monero-project/kastelo/hardware/utilities/ziftosma/README.md

## ZIF/SMA breakout board

This is a ZIF connector to SMA connector breakout board, for testing the NFC and BT antennas.

The following layer definition is used:
<br />
boardname.GTL	 	Top Layer <br />
boardname.GBL	 	Bottom Layer <br />
boardname.GTS	 	Top Soldermask <br />
boardname.GBS	 	Bottom Soldermask <br />
boardname.GTO	 	Top Silkscreen <br />
boardname.GBO	 	Bottom Silkscreen <br />
boardname.GKO	 	Board Outline <br />
boardname.XLN	 	Drills <br />
