monero-project/kastelo/enclosure/breakneck/fabmesh/README.md

## Manufacturing mesh archives

This contains STL and other mesh archives.
