monero-project/kastelo/enclosure/breakneck/fabprnt/README.md

## Printing GCODE archives

This contains GCODE and other machine printing archives.
