monero-project/kastelo/hardware/utilities/flextenna/bluetooth/README.md

## Flexible bluetooth antenna

This a bluetooth antenna designed for being printed on a flexible substrate (Kapton).

Files:
flextenna_bt_kapton5um		Antenna layout optimized for a 5 µm Kapton substrate <br />
(more designs might be added later)

The following layer definition is used:
boardname.GTL	 	Top Layer <br />
boardname.GBL	 	Bottom Layer <br />
boardname.GTS	 	Top Soldermask <br />
boardname.GBS	 	Bottom Soldermask <br />
boardname.GTO	 	Top Silkscreen <br />
boardname.GBO	 	Bottom Silkscreen <br />
boardname.GKO	 	Board Outline <br />
boardname.XLN	 	Drills <br />
