monero-project/kastelo/documents/graphics/promo/README.md

# Promotional Graphics

The Monero Hardware Wallet promotes its brand by making graphics freely available for use in publications.

## Licenses

Artists have contributed their work according to the [Attribution-NonCommercial-ShareAlike 4.0 International license (CC BY-NC-SA 4.0)](https://creativecommons.org/licenses/by-nc-sa/4.0/legalcode).

## Reduced Resolution Equivalents

Locally stored copies of original graphics provide for smaller downloads with reduced resolution.

[Monezor 0.2.0](https://github.com/monero-project/kastelo/tree/master/hardware/monezor/)  
[Monezor 0.2.0](https://github.com/monero-project/kastelo/tree/master/hardware/monezor/)  
[Monezor 0.2.0](https://github.com/monero-project/kastelo/tree/master/hardware/monezor/)  
[Monezor 0.2.0](https://github.com/monero-project/kastelo/tree/master/hardware/monezor/)

## Original Graphics Archives

Artist original graphics are not tracked in revision control but are part of [project releases](https://github.com/monero-project/kastelo/releases/).
