monero-project/kastelo/firmware/monezor/src/bitmaps.c

#include "bitmaps.h"

const uint8_t bmp_digit0_data[] = { 0xff, 0xff, 0xf8, 0x1f, 0xf0, 0x0f, 0xe1, 0x87, 0xe1, 0x87, 0xe1, 0x87, 0xe1, 0x87, 0xe1, 0x87, 0xe1, 0x87, 0xe1, 0x87, 0xe1, 0x87, 0xe1, 0x87, 0xe1, 0x87, 0xf0, 0x0f, 0xf8, 0x1f, 0xff, 0xff, };
const uint8_t bmp_digit1_data[] = { 0xff, 0xff, 0xfc, 0x3f, 0xf8, 0x3f, 0xf0, 0x3f, 0xf0, 0x3f, 0xfc, 0x3f, 0xfc, 0x3f, 0xfc, 0x3f, 0xfc, 0x3f, 0xfc, 0x3f, 0xfc, 0x3f, 0xfc, 0x3f, 0xfc, 0x3f, 0xfc, 0x3f, 0xfc, 0x3f, 0xff, 0xff, };
const uint8_t bmp_digit2_data[] = { 0xff, 0xff, 0xe0, 0x1f, 0xe0, 0x0f, 0xff, 0x87, 0xff, 0x87, 0xff, 0x87, 0xff, 0x87, 0xf8, 0x0f, 0xf0, 0x1f, 0xe1, 0xff, 0xe1, 0xff, 0xe1, 0xff, 0xe1, 0xff, 0xe0, 0x07, 0xe0, 0x07, 0xff, 0xff, };
const uint8_t bmp_digit3_data[] = { 0xff, 0xff, 0xe0, 0x1f, 0xe0, 0x0f, 0xff, 0x87, 0xff, 0x87, 0xff, 0x87, 0xff, 0x87, 0xf8, 0x0f, 0xf8, 0x0f, 0xff, 0x87, 0xff, 0x87, 0xff, 0x87, 0xff, 0x87, 0xe0, 0x0f, 0xe0, 0x1f, 0xff, 0xff, };
const uint8_t bmp_digit4_data[] = { 0xff, 0xff, 0xff, 0x0f, 0xfe, 0x0f, 0xfc, 0x0f, 0xf8, 0x0f, 0xf1, 0x0f, 0xe3, 0x0f, 0xc7, 0x0f, 0xcf, 0x0f, 0xc0, 0x0f, 0xc0, 0x0f, 0xff, 0x0f, 0xff, 0x0f, 0xff, 0x0f, 0xff, 0x0f, 0xff, 0xff, };
const uint8_t bmp_digit5_data[] = { 0xff, 0xff, 0xe0, 0x1f, 0xe0, 0x1f, 0xe7, 0xff, 0xe7, 0xff, 0xe0, 0x1f, 0xe0, 0x0f, 0xff, 0x87, 0xff, 0x87, 0xff, 0x87, 0xff, 0x87, 0xff, 0x87, 0xff, 0x87, 0xe0, 0x0f, 0xe0, 0x1f, 0xff, 0xff, };
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
const uint8_t bmp_u2f_yubico_data[] = { 0x00, 0x1f, 0xf8, 0x00, 0x00, 0x7f, 0xfe, 0x00, 0x01, 0xff, 0xff, 0x80, 0x03, 0xfc, 0x3f, 0xc0, 0x07, 0xe0, 0x07, 0xe0, 0x0f, 0x80, 0x01, 0xf0, 0x1f, 0x00, 0x00, 0x78, 0x3e, 0x00, 0x00, 0x3c, 0x3c, 0x7c, 0x1f, 0x3c, 0x78, 0x7c, 0x1f, 0x1e, 0x78, 0x7c, 0x3e, 0x0e, 0xf0, 0x3e, 0x3e, 0x0f, 0xf0, 0x3e, 0x3c, 0x0f, 0xf0, 0x1f, 0x7c, 0x0f, 0xe0, 0x1f, 0x7c, 0x07, 0xe0, 0x1f, 0x78, 0x07, 0xe0, 0x0f, 0xf8, 0x07, 0xe0, 0x0f, 0xf0, 0x07, 0xf0, 0x0f, 0xf0, 0x0f, 0xf0, 0x07, 0xf0, 0x0f, 0xf0, 0x07, 0xe0, 0x0f, 0x78, 0x03, 0xe0, 0x0e, 0x78, 0x07, 0xc0, 0x1e, 0x3c, 0x07, 0xc0, 0x3e, 0x3c, 0x0f, 0xc0, 0x3c, 0x1e, 0x0f, 0x80, 0x78, 0x0f, 0x8f, 0x81, 0xf0, 0x07, 0xc0, 0x03, 0xe0, 0x03, 0xfc, 0x3f, 0xc0, 0x01, 0xff, 0xff, 0x80, 0x00, 0x7f, 0xff, 0x00, 0x00, 0x1f, 0xf8, 0x00, };

const BITMAP bmp_digit0 = {16, 16, bmp_digit0_data};
const BITMAP bmp_digit1 = {16, 16, bmp_digit1_data};
const BITMAP bmp_digit2 = {16, 16, bmp_digit2_data};
const BITMAP bmp_digit3 = {16, 16, bmp_digit3_data};
const BITMAP bmp_digit4 = {16, 16, bmp_digit4_data};
const BITMAP bmp_digit5 = {16, 16, bmp_digit5_data};
const BITMAP bmp_digit6 = {16, 16, bmp_digit6_data};
const BITMAP bmp_digit7 = {16, 16, bmp_digit7_data};
const BITMAP bmp_digit8 = {16, 16, bmp_digit8_data};
const BITMAP bmp_digit9 = {16, 16, bmp_digit9_data};
const BITMAP bmp_gears0 = {48, 48, bmp_gears0_data};
const BITMAP bmp_gears1 = {48, 48, bmp_gears1_data};
const BITMAP bmp_gears2 = {48, 48, bmp_gears2_data};
const BITMAP bmp_gears3 = {48, 48, bmp_gears3_data};
const BITMAP bmp_icon_error = {16, 16, bmp_icon_error_data};
const BITMAP bmp_icon_info = {16, 16, bmp_icon_info_data};
const BITMAP bmp_icon_ok = {16, 16, bmp_icon_ok_data};
const BITMAP bmp_icon_question = {16, 16, bmp_icon_question_data};
const BITMAP bmp_icon_warning = {16, 16, bmp_icon_warning_data};
const BITMAP bmp_logo48 = {40, 48, bmp_logo48_data};
const BITMAP bmp_logo48_empty = {40, 48, bmp_logo48_empty_data};
const BITMAP bmp_logo64 = {40, 48, bmp_logo64_data};
const BITMAP bmp_logo64_empty = {40, 48, bmp_logo64_empty_data};
const BITMAP bmp_u2f_bitbucket = {32, 32, bmp_u2f_bitbucket_data};
const BITMAP bmp_u2f_bitfinex = {32, 32, bmp_u2f_bitfinex_data};
const BITMAP bmp_u2f_dropbox = {32, 32, bmp_u2f_dropbox_data};
const BITMAP bmp_u2f_fastmail = {32, 32, bmp_u2f_fastmail_data};
const BITMAP bmp_u2f_gandi = {32, 32, bmp_u2f_gandi_data};
const BITMAP bmp_u2f_github = {32, 32, bmp_u2f_github_data};
const BITMAP bmp_u2f_gitlab = {32, 32, bmp_u2f_gitlab_data};
const BITMAP bmp_u2f_google = {32, 32, bmp_u2f_google_data};
const BITMAP bmp_u2f_slushpool = {32, 32, bmp_u2f_slushpool_data};
const BITMAP bmp_u2f_yubico = {32, 32, bmp_u2f_yubico_data};
